digitalepidemiologylab/openbeacon-case/CaseEuroSide.jpg

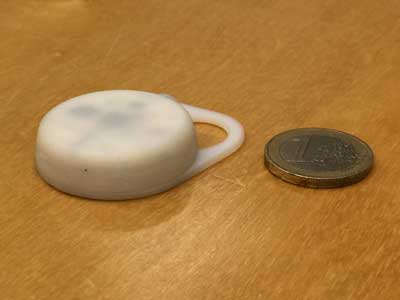
CaseEuroSide.jpg
