digitalepidemiologylab/openbeacon-case/Preview.png

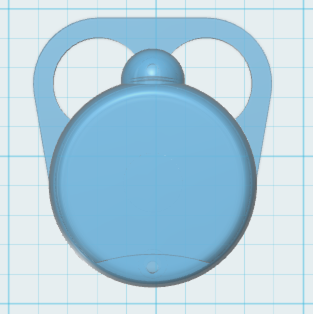
Preview.png
